danenicol/LiteChip-8/LiteChip-8_V1.kicad_sch

## KiCad design LiteChip-8_V1.kicad_sch (2024-05-31)

Schematic: LiteChip-8_V1.kicad_sch

Parts:
C1, C2: C_Polarized_Small_US
D1, D2, D3, D4, D5, D6, D7, D8: CQY99; LED_D5.0mm_IRGrey
R1, R2, R3, R4, R5, R6, R7, R8: 1k ohm
R9: 36k ohm
R10: 18k ohm
SW1, SW2, SW3, SW4, SW5, SW6, SW7, SW8, SW9, SW10, SW11, SW12, SW13, SW14, SW15, SW16, SW17, SW18, SW19, SW20: SW_DPST_x2
U1, U2, U3, U8, U50, U53, U56, U57, U58, U59, U60: (no value)
U4, U14, U15, U18, U19, U35, U36, U39, U40, U44, U45, U47, U48: 74LS173
U5, U13, U16, U17, U20, U37, U38, U41, U42, U43, U46, U51, U54, U55, U61, U62, U63, U64: 74AHC1G04
U6, U21, U22, U33, U34: U
U7: 74LS158
U9, U10: ISOW7742; SOIC-20W_7.5x12.8mm_P1.27mm
U11, U12: 74AHC04
U23, U24: 74LS83
U25, U26, U27, U28, U29, U30, U31, U32: 74AHC1G86
U49: 555 Timer; SOIC-8_3.9x4.9mm_P1.27mm
U52, U65, U66, U67, U68, U69, U70, U71, U72, U73, U74, U75, U76, U77, U78, U95, U96, U97, U98, U99, U100, U102, U103, U104, U106, U107, U108, U110, U111, U112, U114, U115, U116, U118, U119, U120, U122, U133, U134, U135, U137, U138, U139, U140, U142, U143, U144, U145, U147, U148, U149, U151, U153, U154, U155, U157, U159, U160, U162: 74LS21
U101, U105, U109, U113, U117, U121, U136, U141, U146, U152, U156, U158, U161, U163: 4072

Connections:
+5V: R9.2, U1.14 (VCC), U2.14 (VCC), U3.14 (VCC), U4.16 (VCC), U5.5 (VCC), U6.14 (VCC), U7.16 (VCC), U8.14 (VCC), U9.16 (VCC), U10.16 (VCC), U11.14 (VCC), U12.14 (VCC), U13.5 (VCC), U14.16 (VCC), U15.16 (VCC), U16.5 (VCC), U17.5 (VCC), U18.16 (VCC), U19.16 (VCC), U20.5 (VCC), U21.14 (VCC), U22.14 (VCC), U23.16 (VCC), U24.16 (VCC), U25.5 (VCC), U26.5 (VCC), U27.5 (VCC), U28.5 (VCC), U29.5 (VCC), U30.5 (VCC), U31.5 (VCC), U32.5 (VCC), U33.14 (VCC), U34.14 (VCC), U35.16 (VCC), U36.16 (VCC), U37.5 (VCC), U38.5 (VCC), U39.16 (VCC), U40.16 (VCC), U41.5 (VCC), U42.5 (VCC), U43.5 (VCC), U44.16 (VCC), U45.16 (VCC), U46.5 (VCC), U47.16 (VCC), U48.16 (VCC), U49.4 (R), U49.8 (VCC), U50.14 (VCC), U51.5 (VCC), U52.2 (GND), U53.14 (VCC), U54.5 (VCC), U55.5 (VCC), U56.14 (VCC), U57.14 (VCC), U58.14 (VCC), U59.14 (VCC), U60.14 (VCC), U61.5 (VCC), U62.5 (VCC), U63.5 (VCC), U64.5 (VCC), U65.2 (GND), U66.2 (GND), U67.2 (GND), U68.2 (GND), U69.2 (GND), U70.2 (GND), U71.2 (GND), U72.2 (GND), U73.2 (GND), U74.2 (GND), U75.2 (GND), U76.2 (GND), U77.2 (GND), U78.2 (GND)
Earth: C1.2, C2.2, D1.1 (K), D2.1 (K), D3.1 (K), D4.1 (K), D5.1 (K), D6.1 (K), D7.1 (K), D8.1 (K), SW1.1 (A), SW2.1 (A), SW3.1 (A), SW4.1 (A), SW5.1 (A), SW6.1 (A), SW7.1 (A), SW8.1 (A), SW9.1 (A), SW10.1 (A), SW11.1 (A), SW12.1 (A), SW13.1 (A), SW14.1 (A), SW15.1 (A), SW16.1 (A), SW17.1 (A), SW18.1 (A), SW19.1 (A), SW20.1 (A), U1.7 (GND), U2.7 (GND), U3.7 (GND), U4.1 (M), U4.2 (N), U4.8 (GND), U4.15 (CLR), U5.3 (GND), U6.7 (GND), U7.8 (GND), U7.15 (`G), U8.7 (GND), U9.8 (GND), U10.8 (GND), U11.7 (GND), U12.7 (GND), U13.3 (GND), U14.8 (GND), U14.15 (CLR), U15.1 (M), U15.2 (N), U15.8 (GND), U16.3 (GND), U17.3 (GND), U18.1 (M), U18.2 (N), U18.8 (GND), U18.15 (CLR), U19.1 (M), U19.2 (N), U19.8 (GND), U19.15 (CLR), U20.3 (GND), U21.7 (GND), U22.7 (GND), U23.8 (GND), U24.8 (GND), U25.3 (GND), U26.3 (GND), U27.3 (GND), U28.3 (GND), U29.3 (GND), U30.3 (GND), U31.3 (GND), U32.3 (GND), U33.7 (GND), U34.7 (GND), U35.1 (M), U35.2 (N), U35.8 (GND), U35.15 (CLR), U36.1 (M), U36.2 (N), U36.8 (GND), U36.15 (CLR), U37.3 (GND), U38.3 (GND), U39.8 (GND), U39.15 (CLR), U40.8 (GND), U40.15 (CLR), U41.3 (GND), U42.3 (GND), U43.3 (GND), U44.8 (GND), U44.15 (CLR), U45.8 (GND), U45.15 (CLR), U46.3 (GND), U47.1 (M), U47.2 (N), U47.8 (GND), U47.15 (CLR), U48.1 (M), U48.2 (N), U48.8 (GND), U48.15 (CLR), U49.1 (GND), U50.7 (GND), U51.3 (GND), U52.2 (GND), U53.7 (GND), U54.3 (GND), U55.3 (GND), U56.1 (J_1), U56.7 (GND), U57.3 (Q_1), U57.7 (GND), U58.7 (GND), U59.7 (GND), U60.7 (GND), U61.3 (GND), U62.3 (GND), U63.3 (GND), U64.3 (GND), U65.2 (GND), U66.2 (GND), U67.2 (GND), U68.2 (GND), U69.2 (GND), U70.2 (GND), U71.2 (GND), U72.2 (GND), U73.2 (GND), U74.2 (GND), U75.2 (GND), U76.2 (GND), U77.2 (GND), U78.2 (GND), U95.1, U96.1, U97.1, U98.1, U99.1, U100.1, U102.1, U107.1, U108.1, U110.1, U111.1, U112.1, U114.1, U115.1, U116.1, U118.1, U120.1, U122.1, U138.1, U139.1, U140.1, U142.1, U143.1, U144.1, U145.1, U147.1, U155.1, U157.1, U159.1
unnamed: C1.1, R10.1, U49.2 (TR), U49.6 (THR)
unnamed: C2.1, U49.5 (CV)
unnamed: D1.2 (A), R1.2
unnamed: D2.2 (A), R2.2
unnamed: D3.2 (A), R3.2
unnamed: D4.2 (A), R4.2
unnamed: D5.2 (A), R5.2
unnamed: D6.2 (A), R6.2
unnamed: D7.2 (A), R7.2
unnamed: D8.2 (A), R8.2
unnamed: R1.1, U47.3 (Q1)
unnamed: R2.1, U47.4 (Q2)
unnamed: R3.1, U47.6 (Q4)
unnamed: R4.1, U47.5 (Q3)
unnamed: R5.1, U48.6 (Q4)
unnamed: R6.1, U48.5 (Q3)
unnamed: R7.1, U48.4 (Q2)
unnamed: R8.1, U48.3 (Q1)
unnamed: R9.1, R10.2, U49.7 (DIS)
unnamed: SW1.2 (B), U9.12 (D4)
unnamed: SW2.2 (B), U9.10 (D3)
unnamed: SW3.2 (B), U9.6 (D2)
unnamed: SW4.2 (B), U9.4 (D1)
unnamed: SW5.2 (B), U10.12 (D4)
unnamed: SW6.2 (B), U10.10 (D3)
unnamed: SW7.2 (B), U10.6 (D2)
unnamed: SW8.2 (B), U10.4 (D1)
unnamed: SW9.2 (B), U9.3 (WE), U10.3 (WE)
unnamed: SW10.2 (B), U9.2 (ME), U10.2 (ME), U13.4
unnamed: SW11.2 (B), U7.3 (B1)
unnamed: SW12.2 (B), U7.6 (B2)
unnamed: SW13.2 (B), U7.10 (3B)
unnamed: SW14.2 (B), U7.13 (B4)
unnamed: SW15.2 (B), U7.1 (`A/B)
unnamed: SW16.2 (B), U50.13 (`CLR_1)
unnamed: SW17.2 (B), U53.13 (`CLR_1), U56.13 (`CLR_1), U57.13 (`CLR_1), U58.13 (`CLR_1), U60.13 (`CLR_1)
unnamed: SW18.2 (B), U1.13 (`CLR_1), U2.13 (`CLR_1), U3.13 (`CLR_1), U8.13 (`CLR_1)
unnamed: SW19.2 (B), U15.15 (CLR)
unnamed: SW20.2 (B), U51.2, U78.5
unnamed: U1.1 (J_1), U1.4 (K_1), U2.1 (J_1), U2.4 (K_1), U3.1 (J_1), U3.4 (K_1), U8.1 (J_1), U8.4 (K_1), U58.1 (J_1), U59.3 (Q_1)
unnamed: U1.3 (Q_1), U6.9 (3A), U8.12 (CLK_1)
unnamed: U1.12 (CLK_1), U2.3 (Q_1), U6.5 (2A)
unnamed: U2.12 (CLK_1), U3.3 (Q_1), U6.2 (1A)
unnamed: U4.3 (Q1), U7.2 (A1)
unnamed: U4.4 (Q2), U7.5 (A2)
unnamed: U4.5 (Q3), U7.11 (3A)
unnamed: U4.6 (Q4), U7.14 (A4)
unnamed: U4.9 (`G1), U4.10 (`G2), U5.4
unnamed: U6.12 (4A), U8.3 (Q_1)
unnamed: U7.4 (Y1), U9.1 (A0), U10.1 (A0)
unnamed: U10.5 (S1), U12.1 (A1)
unnamed: U10.7 (S2), U12.3 (A2)
unnamed: U10.9 (S3), U12.5 (A3)
unnamed: U10.11 (S4), U12.9 (A4)
unnamed: U7.12 (Y4), U9.13 (A3), U10.13 (A3)
unnamed: U7.9 (Y3), U9.14 (A2), U10.14 (A2)
unnamed: U7.7 (Y2), U9.15 (A1), U10.15 (A1)
unnamed: U9.5 (S1), U11.1 (A1)
unnamed: U11.2 (Y1), U19.14 (D1), U22.3 (1Y), U34.3 (1Y), U36.14 (D1), U40.3 (Q1), U40.14 (D1), U45.3 (Q1), U45.14 (D1), U48.14 (D1)
unnamed: U9.7 (S2), U11.3 (A2)
unnamed: U11.4 (Y2), U15.13 (D2), U19.13 (D2), U22.6 (2Y), U34.6 (2Y), U36.13 (D2), U40.4 (Q2), U40.13 (D2), U45.4 (Q2), U45.13 (D2), U48.13 (D2)
unnamed: U9.9 (S3), U11.5 (A3)
unnamed: U11.6 (Y3), U15.12 (D3), U19.12 (D3), U22.8 (3Y), U34.8 (3Y), U36.12 (D3), U40.5 (Q3), U40.12 (D3), U45.5 (Q3), U45.12 (D3), U48.12 (D3)
unnamed: U11.8 (Y4), U15.11 (D4), U19.11 (D4), U22.11 (4Y), U34.11 (4Y), U36.11 (D4), U40.6 (Q4), U40.11 (D4), U45.6 (Q4), U45.11 (D4), U48.11 (D4)
unnamed: U9.11 (S4), U11.9 (A4)
unnamed: U6.3 (1Y), U12.2 (Y1), U14.6 (Q4), U18.14 (D1), U21.3 (1Y), U33.3 (1Y), U35.14 (D1), U39.3 (Q1), U39.14 (D1), U44.3 (Q1), U44.14 (D1), U47.14 (D1)
unnamed: U4.13 (D2), U6.6 (2Y), U12.4 (Y2), U14.5 (Q3), U14.13 (D2), U18.13 (D2), U21.6 (2Y), U33.6 (2Y), U35.13 (D2), U39.4 (Q2), U39.13 (D2), U44.4 (Q2), U44.13 (D2), U47.13 (D2)
unnamed: U4.12 (D3), U6.8 (3Y), U12.6 (Y3), U14.4 (Q2), U14.12 (D3), U18.12 (D3), U21.8 (3Y), U33.8 (3Y), U35.12 (D3), U39.5 (Q3), U39.12 (D3), U44.5 (Q3), U44.12 (D3), U47.12 (D3)
unnamed: U4.11 (D4), U6.11 (4Y), U12.8 (Y4), U14.3 (Q1), U14.11 (D4), U18.11 (D4), U21.11 (4Y), U33.11 (4Y), U35.11 (D4), U39.6 (Q4), U39.11 (D4), U44.6 (Q4), U44.11 (D4), U47.11 (D4)
unnamed: U14.1 (M), U14.2 (N), U17.4
unnamed: U3.12 (CLK_1), U4.7 (CLK), U14.7 (CLK), U15.7 (CLK), U18.7 (CLK), U19.7 (CLK), U35.7 (CLK), U36.7 (CLK), U39.7 (CLK), U40.7 (CLK), U44.7 (CLK), U45.7 (CLK), U47.7 (CLK), U48.7 (CLK), U53.12 (CLK_1), U54.4, U56.12 (CLK_1), U57.12 (CLK_1), U58.12 (CLK_1), U60.12 (CLK_1)
unnamed: U14.9 (`G1), U14.10 (`G2), U15.9 (`G1), U15.10 (`G2), U16.4
unnamed: U15.3 (Q1), U52.1, U64.2, U66.1, U68.1, U70.1, U73.1, U75.1, U76.1, U78.1
unnamed: U15.4 (Q2), U52.2 (GND), U63.2, U65.2 (GND), U68.2 (GND), U69.2 (GND), U74.2 (GND), U75.2 (GND), U78.2 (GND)
unnamed: U15.5 (Q3), U52.3, U62.2, U65.3, U66.3, U67.3, U76.3, U77.3, U78.3
unnamed: U15.6 (Q4), U61.2, U72.4, U73.4, U74.4, U75.4, U76.4, U77.4, U78.4
unnamed: U18.3 (Q1), U21.2 (1A), U23.5 (A1)
unnamed: U18.4 (Q2), U21.5 (2A), U23.3 (A2)
unnamed: U18.5 (Q3), U21.9 (3A), U23.14 (A3)
unnamed: U18.6 (Q4), U21.12 (4A), U23.12 (A4)
unnamed: U18.9 (`G1), U18.10 (`G2), U19.9 (`G1), U19.10 (`G2), U20.4
unnamed: U19.3 (Q1), U22.2 (1A), U24.5 (A1)
unnamed: U19.4 (Q2), U22.5 (2A), U24.3 (A2)
unnamed: U19.5 (Q3), U22.9 (3A), U24.14 (A3)
unnamed: U19.6 (Q4), U22.12 (4A), U24.12 (A4)
unnamed: U23.1 (Σ2), U33.5 (2A)
unnamed: U23.2 (B2), U30.4
unnamed: U23.4 (Σ1), U33.2 (1A)
unnamed: U23.6 (B1), U29.4
unnamed: U23.10 (Σ4), U33.12 (4A)
unnamed: U23.11 (B4), U32.4
unnamed: U23.13 (Σ3), U33.9 (3A)
unnamed: U23.14 (A3), U24.7 (C0)
unnamed: U23.15 (B3), U31.4
unnamed: U24.1 (Σ2), U34.5 (2A)
unnamed: U24.2 (B2), U27.4
unnamed: U24.4 (Σ1), U34.2 (1A)
unnamed: U24.6 (B1), U28.4
unnamed: U24.10 (Σ4), U34.12 (4A)
unnamed: U24.11 (B4), U25.4
unnamed: U24.13 (Σ3), U34.9 (3A)
unnamed: U24.15 (B3), U26.4
unnamed: U25.1, U36.6 (Q4)
unnamed: U26.1, U36.5 (Q3)
unnamed: U27.1, U36.4 (Q2)
unnamed: U28.1, U36.3 (Q1)
unnamed: U29.1, U35.3 (Q1)
unnamed: U30.1, U35.4 (Q2)
unnamed: U31.1, U35.5 (Q3)
unnamed: U32.1, U35.6 (Q4)
unnamed: U35.9 (`G1), U35.10 (`G2), U36.9 (`G1), U36.10 (`G2), U37.4
unnamed: U38.4, U39.9 (`G1), U39.10 (`G2), U40.9 (`G1), U40.10 (`G2)
unnamed: U39.1 (M), U39.2 (N), U40.1 (M), U40.2 (N), U41.4
unnamed: U42.4, U44.1 (M), U44.2 (N), U45.1 (M), U45.2 (N)
unnamed: U43.4, U44.9 (`G1), U44.10 (`G2), U45.9 (`G1), U45.10 (`G2)
unnamed: U46.2, U98.5
unnamed: U46.4, U47.9 (`G1), U47.10 (`G2), U48.9 (`G1), U48.10 (`G2)
unnamed: U49.3 (Q), U50.12 (CLK_1)
unnamed: U50.1 (J_1), U50.4 (K_1), U51.4
unnamed: U50.3 (Q_1), U55.2
unnamed: U52.4, U61.4, U65.4, U66.4, U67.4, U68.4, U69.4, U70.4, U71.4
unnamed: U53.2 (`Q_1), U60.4 (K_1)
unnamed: U53.4 (K_1), U56.2 (`Q_1)
unnamed: U54.2, U55.4
unnamed: U56.4 (K_1), U57.2 (`Q_1)
unnamed: U57.4 (K_1), U58.2 (`Q_1)
unnamed: U58.4 (K_1), U59.2 (`Q_1)
unnamed: U59.4 (K_1), U60.2 (`Q_1)
unnamed: U62.4, U68.3, U69.3, U70.3, U71.3, U72.3, U73.3, U74.3, U75.3
unnamed: U63.4, U66.2 (GND), U67.2 (GND), U70.2 (GND), U71.2 (GND), U72.2 (GND), U73.2 (GND), U76.2 (GND), U77.2 (GND)
unnamed: U64.4, U65.1, U67.1, U69.1, U71.1, U72.1, U74.1, U77.1
unnamed: U95.2 (GND), U96.2 (GND), U97.2 (GND), U98.2 (GND), U99.2 (GND), U100.2 (GND), U101.1 (GND), U102.2 (GND), U103.2 (GND), U104.2 (GND), U105.1 (GND), U106.2 (GND), U107.2 (GND), U108.2 (GND), U109.1 (GND), U110.2 (GND), U111.2 (GND), U112.2 (GND), U113.1 (GND), U114.2 (GND), U115.2 (GND), U116.2 (GND), U117.1 (GND), U118.2 (GND), U119.2 (GND), U120.2 (GND), U121.1 (GND), U122.2 (GND), U133.2 (GND), U134.2 (GND), U135.2 (GND), U136.1 (GND), U137.2 (GND), U138.2 (GND), U139.2 (GND), U140.2 (GND), U141.1 (GND), U142.2 (GND), U143.2 (GND), U144.2 (GND), U145.2 (GND), U146.1 (GND), U147.2 (GND), U148.2 (GND), U149.2 (GND), U151.2 (GND), U152.1 (GND), U153.2 (GND), U154.2 (GND), U155.2 (GND), U156.1 (GND), U157.2 (GND), U158.1 (GND), U159.2 (GND), U160.2 (GND), U161.1 (GND), U162.2 (GND), U163.1 (GND)
unnamed: U66.5, U100.4, U104.4, U108.4, U115.4
unnamed: U100.5, U101.3
unnamed: U5.2, U101.1 (GND)
unnamed: U101.2, U102.5
unnamed: U99.5, U101.4
unnamed: U6.1 (1G), U6.4 (2G), U6.10 (3G), U6.13 (4G), U59.1 (J_1), U60.3 (Q_1), U101.5
unnamed: U65.5, U102.4, U106.4, U110.4, U119.4
unnamed: U53.1 (J_1), U56.3 (Q_1), U103.1, U104.1, U106.1, U119.1, U133.1, U134.1, U135.1, U137.1, U148.1, U149.1, U151.1, U153.1, U154.1, U160.1, U162.1
unnamed: U71.5, U99.4, U103.4, U107.4, U148.4
unnamed: U103.5, U105.4
unnamed: U104.5, U105.3
unnamed: U13.2, U105.1 (GND)
unnamed: U105.2, U106.5
unnamed: U16.2, U57.1 (J_1), U58.3 (Q_1), U105.5
unnamed: U107.5, U109.5
unnamed: U108.5, U109.4
unnamed: U17.2, U109.1 (GND)
unnamed: U109.2, U110.5
unnamed: U76.5, U98.4, U111.4
unnamed: U111.5, U113.5
unnamed: U52.5, U112.4, U116.4
unnamed: U112.5, U113.4
unnamed: U21.1 (1G), U21.4 (2G), U21.10 (3G), U21.13 (4G), U22.1 (1G), U22.4 (2G), U22.10 (3G), U22.13 (4G), U113.1 (GND)
unnamed: U113.2, U114.5
unnamed: U72.5, U114.4, U120.4
unnamed: U115.5, U117.5
unnamed: U116.5, U117.4
unnamed: U38.2, U117.1 (GND)
unnamed: U117.2, U118.5
unnamed: U77.5, U118.4, U159.4
unnamed: U119.5, U121.5
unnamed: U120.5, U121.4
unnamed: U43.2, U121.1 (GND)
unnamed: U121.2, U122.5
unnamed: U74.5, U122.4, U147.4
unnamed: U70.5, U133.4, U138.4, U143.4, U149.4
unnamed: U133.5, U136.5
unnamed: U69.5, U95.4, U134.4, U139.4, U151.4
unnamed: U134.5, U136.4
unnamed: U68.5, U135.4, U140.4, U144.4, U153.4, U160.4
unnamed: U135.5, U136.3
unnamed: U33.1 (1G), U33.4 (2G), U33.10 (3G), U33.13 (4G), U34.1 (1G), U34.4 (2G), U34.10 (3G), U34.13 (4G), U136.1 (GND)
unnamed: U136.2, U137.5
unnamed: U67.5, U96.4, U137.4, U142.4, U154.4, U162.4
unnamed: U138.5, U141.5
unnamed: U139.5, U141.4
unnamed: U140.5, U141.3
unnamed: U37.2, U141.1 (GND)
unnamed: U141.2, U142.5
unnamed: U143.5, U146.5
unnamed: U144.5, U146.4
unnamed: U73.5, U145.4, U155.4
unnamed: U145.5, U146.3
unnamed: U41.2, U146.1 (GND)
unnamed: U146.2, U147.5
unnamed: U148.5, U163.5
unnamed: U149.5, U163.4
unnamed: U151.5, U163.2
unnamed: U20.2, U152.1 (GND)
unnamed: U152.2, U156.1 (GND)
unnamed: U152.5, U163.1 (GND)
unnamed: U153.5, U156.5
unnamed: U154.5, U156.4
unnamed: U155.5, U156.3
unnamed: U156.2, U157.5
unnamed: U75.5, U97.4, U157.4
unnamed: U42.2, U158.1 (GND)
unnamed: U158.2, U159.5
unnamed: U97.5, U158.3
unnamed: U96.5, U158.4
unnamed: U95.5, U158.5
unnamed: U160.5, U161.5
unnamed: U23.7 (C0), U25.2, U26.2, U27.2, U28.2, U29.2, U30.2, U31.2, U32.2, U161.1 (GND)
unnamed: U161.2, U162.5
Ring Counter: U53.3 (Q_1), U60.1 (J_1)

Notes on the sheet:
SUB C T5
Closed = Grounded = 0
LED 4
PWR
GND
MVI C
MOV A,C: 1000
Open = Floating = 1
SUB B: 0011
MOV B,C
LED 3
Bit 8
Bit 4
CLR
LDA T4
MOV A,C
MVI C: 0110
Bit 3
MVI B T4
MOV B,C: 1010
HLT
CLK
Bit 1
SUB B
SUB B T4
ADD C: 0010
ADD B
`CLR
MOV C,A T4
ADD C
LiteChip-8
MOV A,B
A = MAR
LDA
MOV B,A
MVI C T5
MOV C,B T4
MOV C,A
OUT
MVI B
SUB C
Closed = Write
Bit 2
1000 htz
SUB C T4
LDA: 0000
HLT: 1111
MVI B: 0101
ADD C T5
LED 6
50% duty cycle
`A/B
MOV A,B: 0111
LED 1
SUB C: 0100
Bit 5
MOV C,B: 1100
MOV C,B
Dane Nicol
Closed = Clear
1111 RAM LIMIT
MVI B T5
MVI C T4
MOV B,A: 1001
Open = Program
MOV B,A T4
Open = Clear
May 30, 2024
Prog/Run
LDA T5
MOV A,C T4
SUB B T5
Closed = Program
ADD B T5
Read/Write
MOV A,B T4
ADD C T4
ADD B T4
Closed = Run
ICR
LED 8
LED 2
Open = Halt
B = Operator
LED 5
ADD B: 0001
Clock Signal
MOV B,C T4
OUT: 1101
OUT T4
Open = Run
MOV C,A: 1011
Data Program Switches
Ring
Open = Read
(RAM on or off)
